mavory/ESP32-Smart-light/Circuit Diagram/ESP32.kicad_sch

## KiCad design Circuit Diagram/ESP32.kicad_sch (2026-01-19)

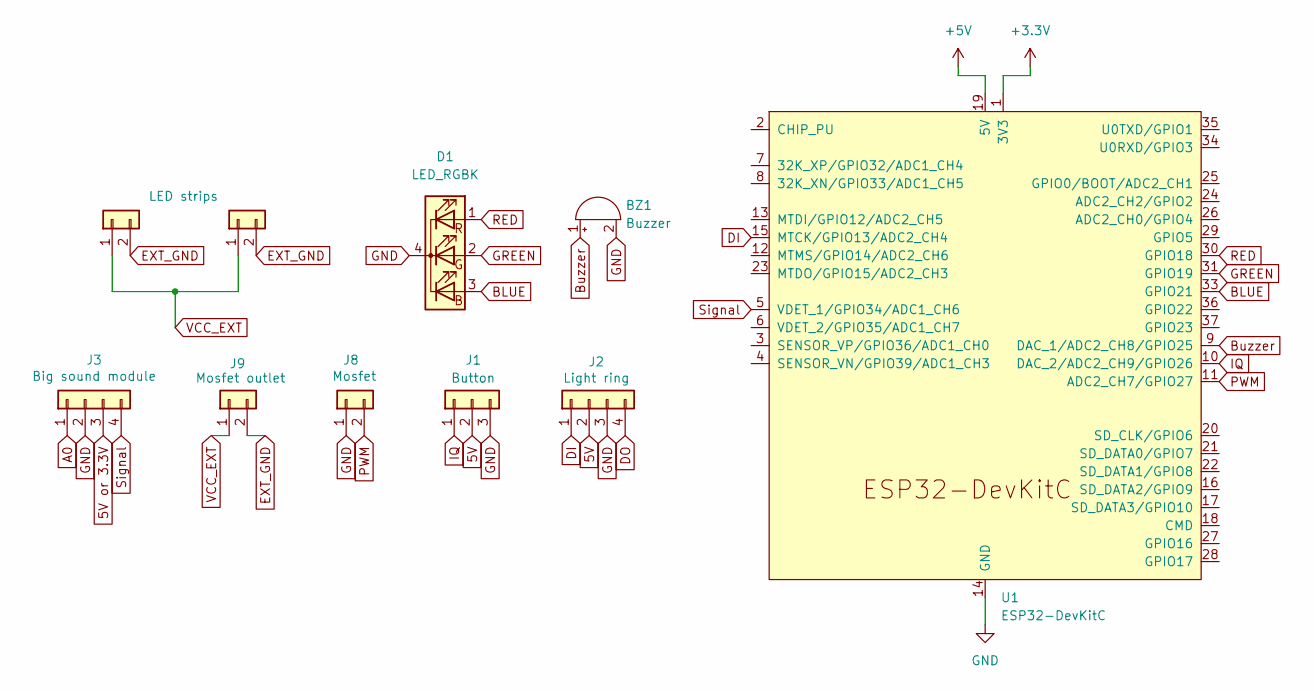
[picture p24: schematic ESP32.kicad_sch]

Parts:
BZ1: Buzzer
D1: LED_RGBK
J1: Button
J2: Light ring
J3: Big sound module
J6: LED strips
J7: Conn_01x02
J8: Mosfet
J9: Mosfet outlet
U1: ESP32-DevKitC

Connections:
5V: J1.2, J2.2
5V or 3.3V: J3.3
+3.3V: U1.1 (3V3)
+5V: U1.19 (5V)
A0: J3.1
BLUE: D1.3 (BA), U1.33 (GPIO21)
Buzzer: BZ1.1 (+), U1.9 (DAC_1/ADC2_CH8/GPIO25)
DI: J2.1, U1.15 (MTCK/GPIO13/ADC2_CH4)
DO: J2.4
EXT_GND: J6.2, J7.2, J9.2
GND: BZ1.2 (-), D1.4 (K), J1.3, J2.3, J3.2, J8.1, U1.14 (GND), U1.32 (GND), U1.38 (GND)
GREEN: D1.2 (GA), U1.31 (GPIO19)
IQ: J1.1, U1.10 (DAC_2/ADC2_CH9/GPIO26)
PWM: J8.2, U1.11 (ADC2_CH7/GPIO27)
RED: D1.1 (RA), U1.30 (GPIO18)
Signal: J3.4, U1.5 (VDET_1/GPIO34/ADC1_CH6)
VCC_EXT: J6.1, J7.1, J9.1
