mavory/ESP32-Smart-light/Photos/20260118_110145.jpg

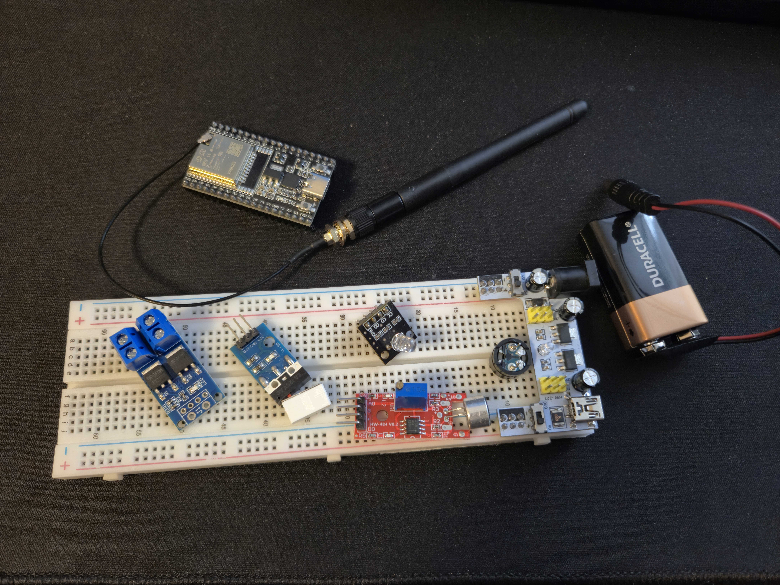
Photos/20260118_110145.jpg
