mavory/ESP32-Smart-light/Photos/20260118_213228.jpg

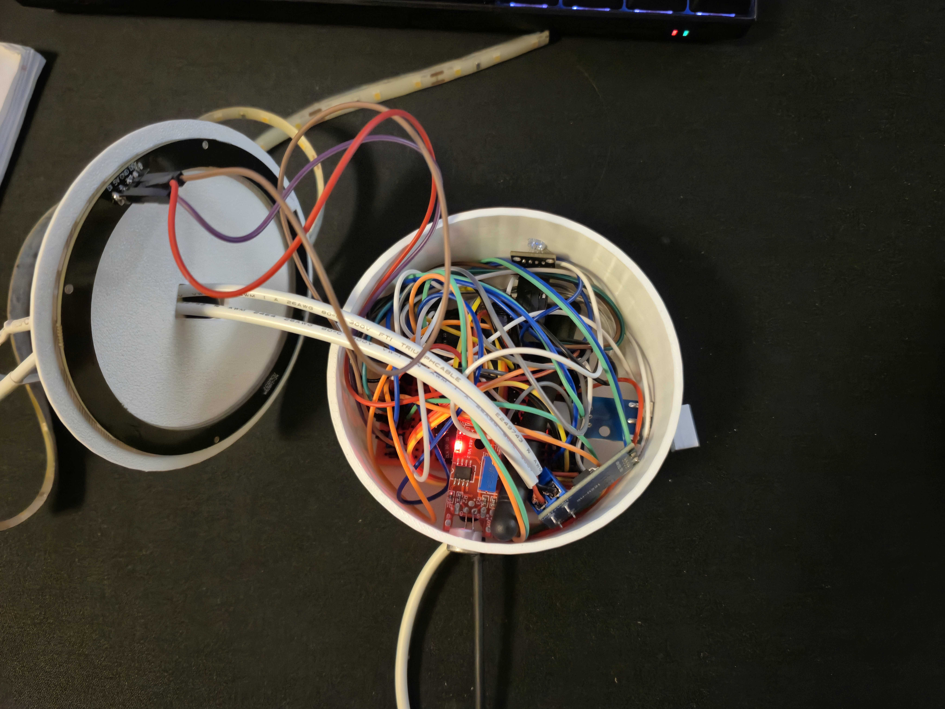
Photos/20260118_213228.jpg
