mavory/ESP32-Smart-light/Photos/20260119_094715 (1).jpg

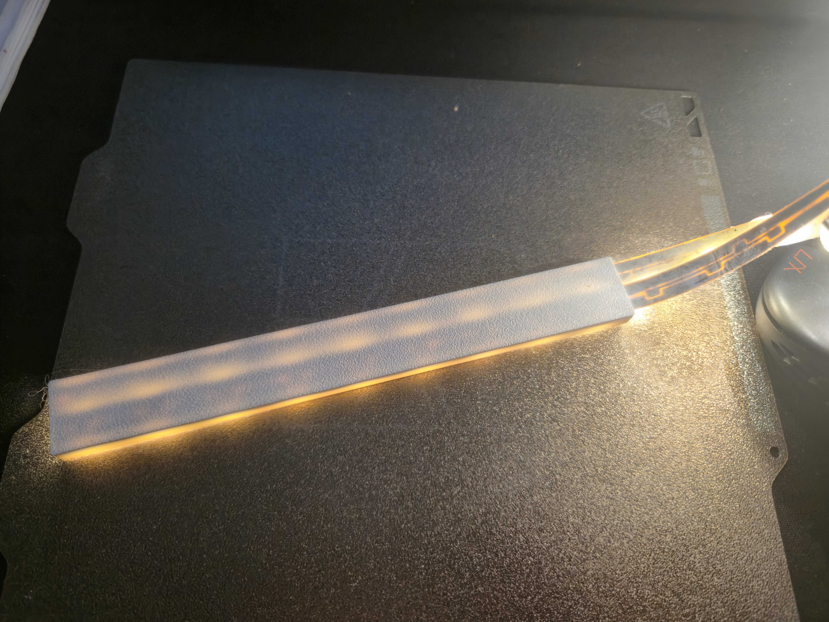
Photos/20260119_094715 (1).jpg
