mavory/ESP32-Smart-light/Photos/20260119_102135.jpg

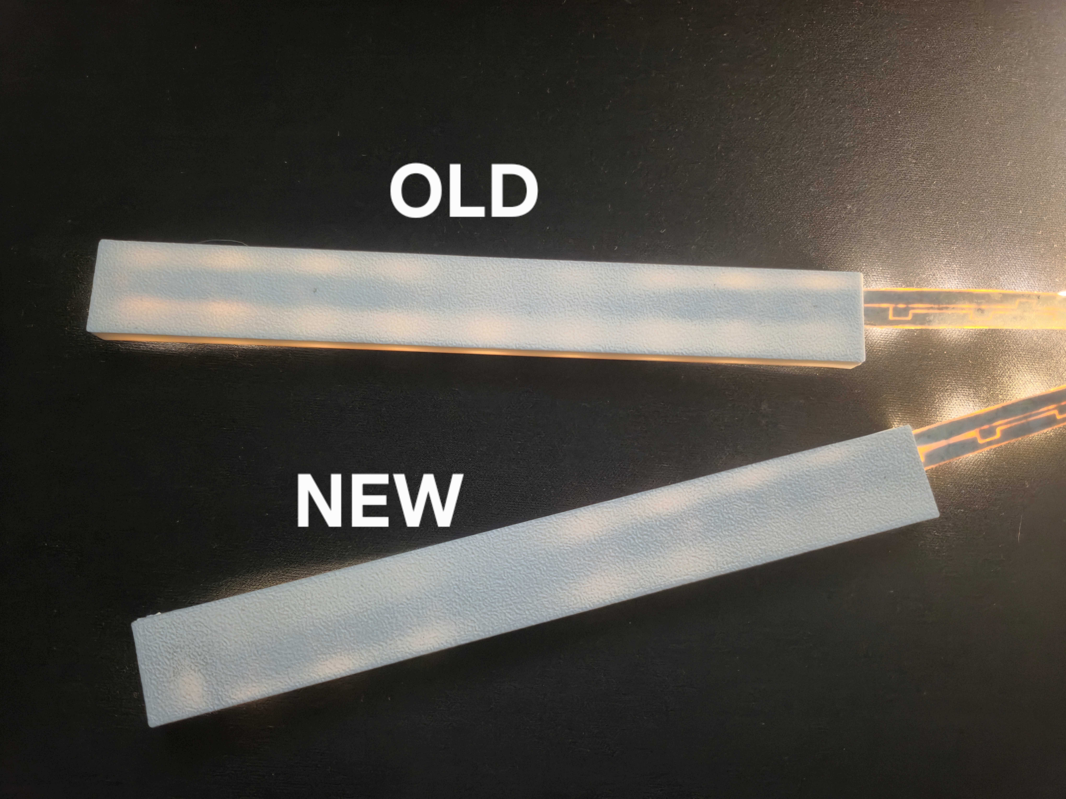
Photos/20260119_102135.jpg
