mavory/ESP32-Smart-light/Photos/20260119_114646 (1).jpg

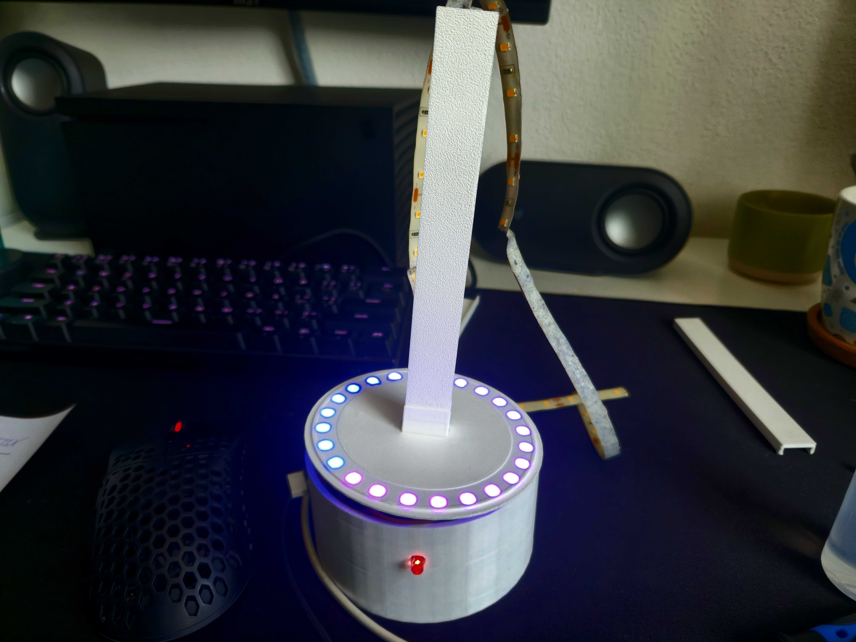
Photos/20260119_114646 (1).jpg
