mavory/ESP32-Smart-light/Photos/20260119_122217.jpg

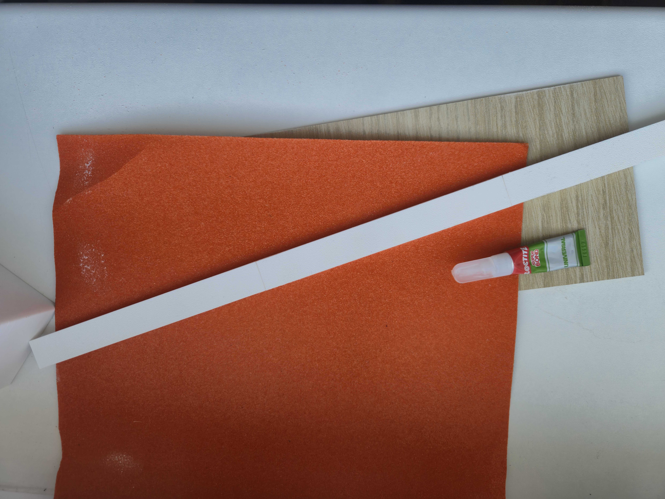
Photos/20260119_122217.jpg
