mavory/ESP32-Smart-light/Photos/20260119_123537.jpg

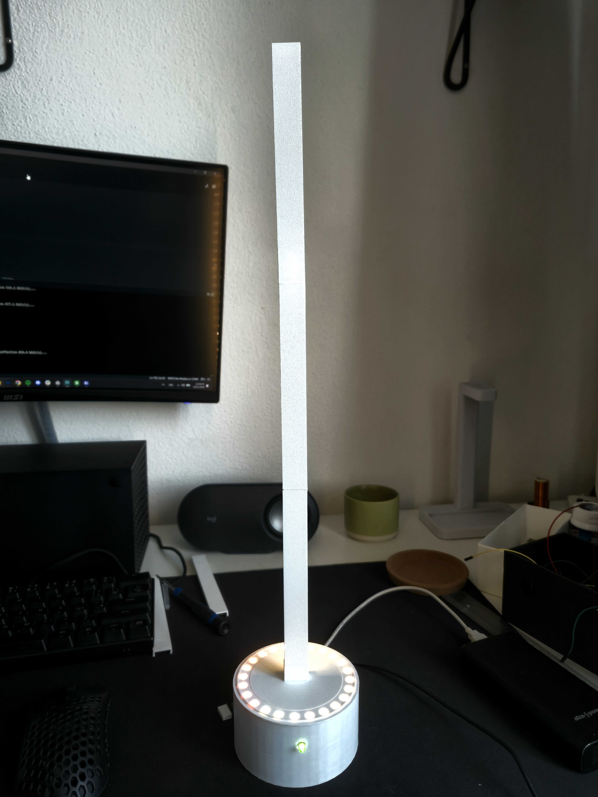
Photos/20260119_123537.jpg
