mavory/ESP32-Smart-light/Photos/1000023968.jpg

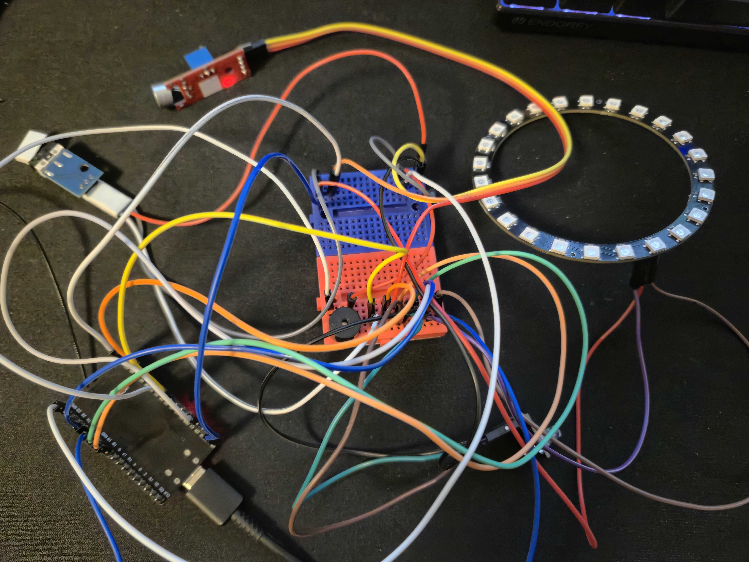
Photos/1000023968.jpg
