mavory/ESP32-Smart-light/Photos/1000023970.jpg

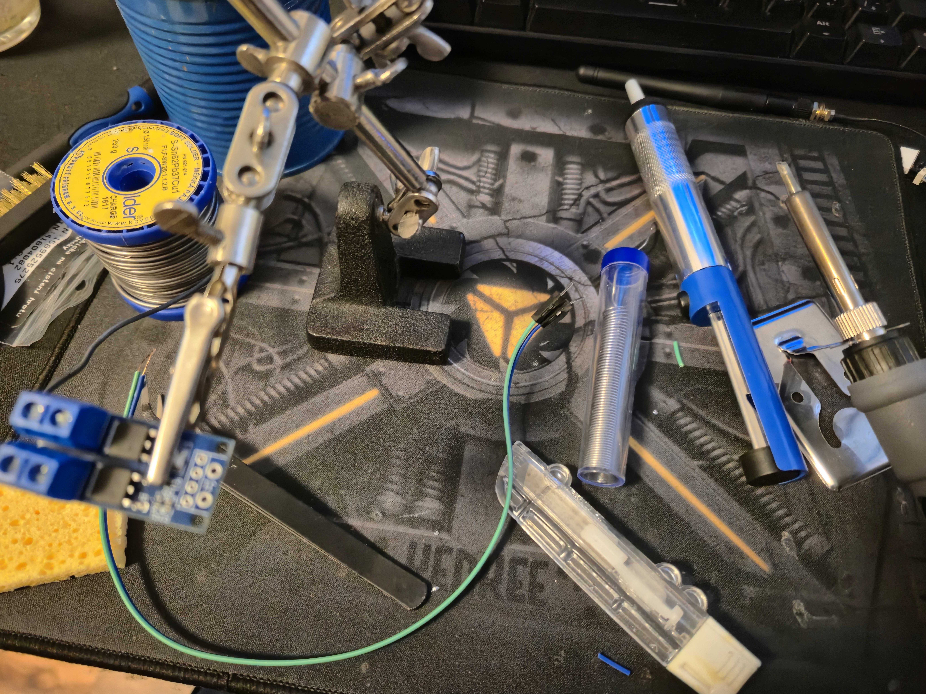
Photos/1000023970.jpg
