mavory/ESP32-Smart-light/Photos/1000023972.jpg

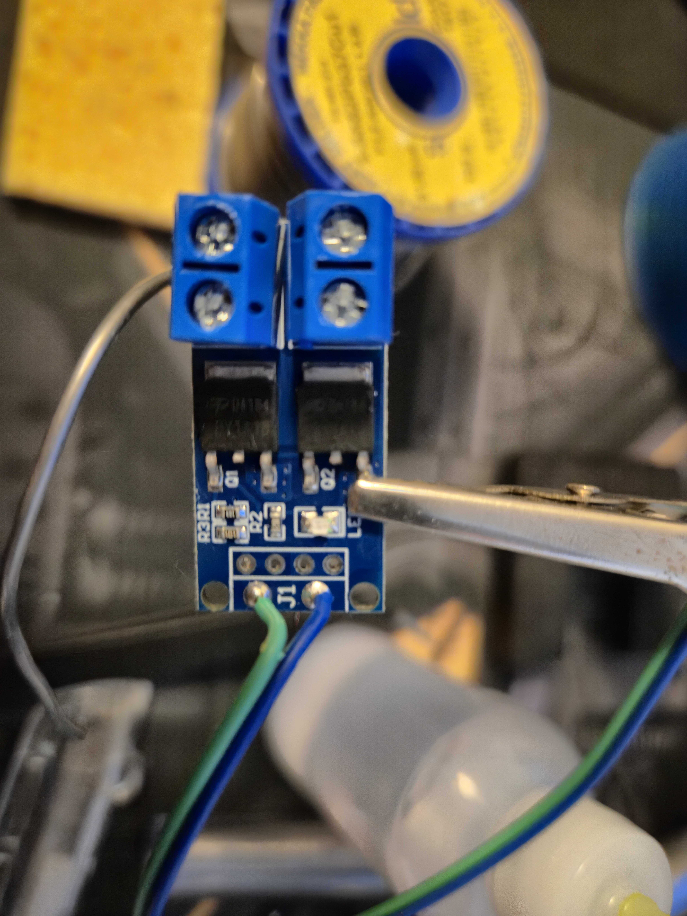
Photos/1000023972.jpg
