mavory/ESP32-Smart-light/Photos/1000023974.jpg

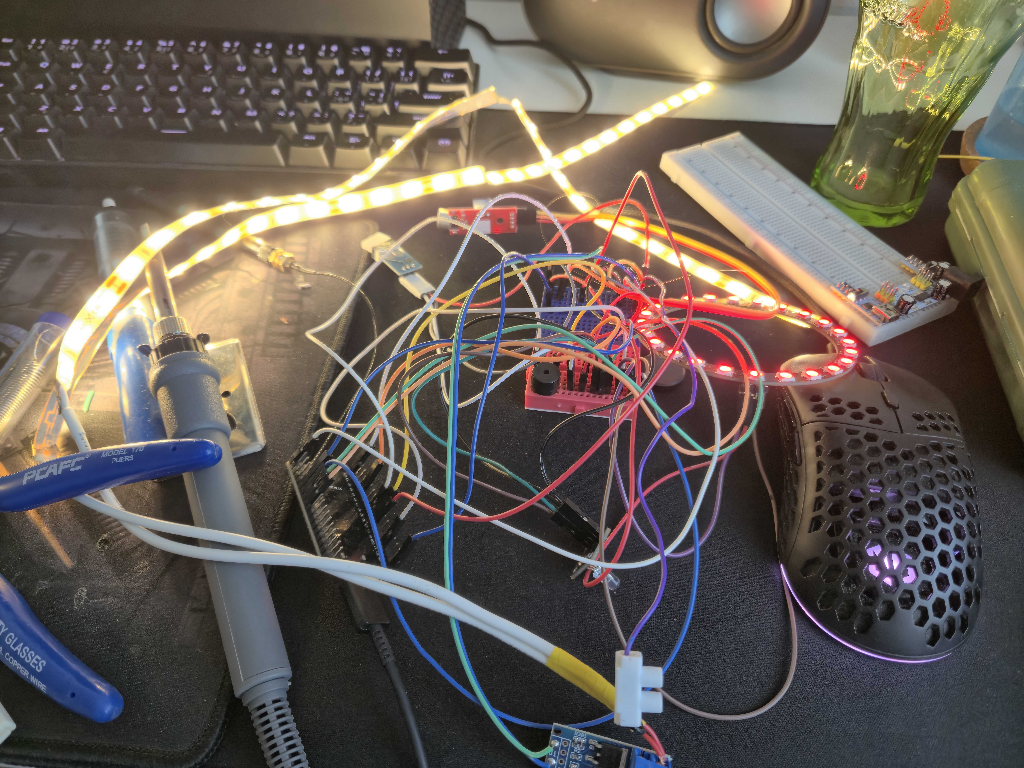
Photos/1000023974.jpg
