mavory/ESP32-Smart-light/Photos/1000023976.jpg

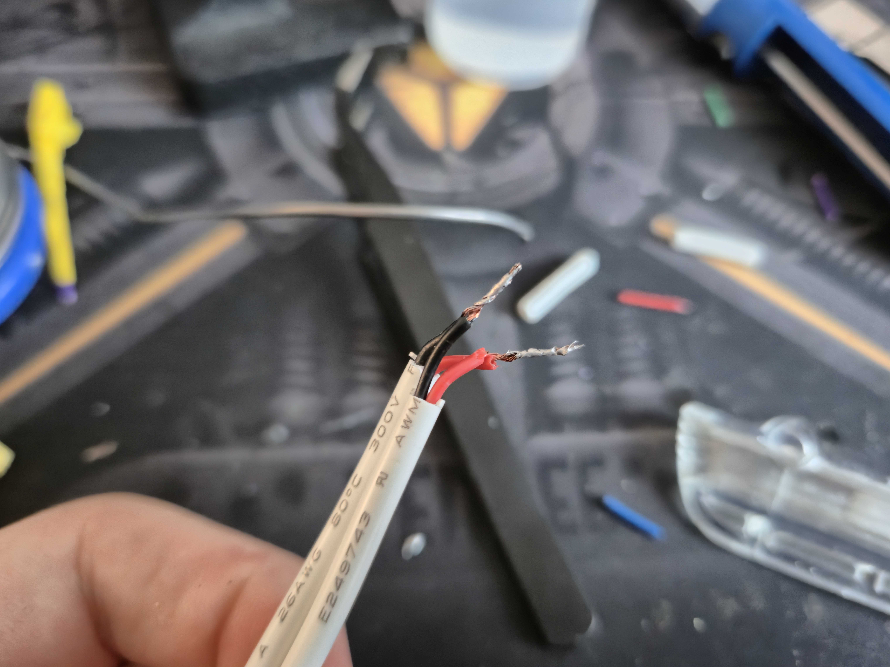
Photos/1000023976.jpg
