mavory/ESP32-Smart-light/Photos/1000023977.jpg

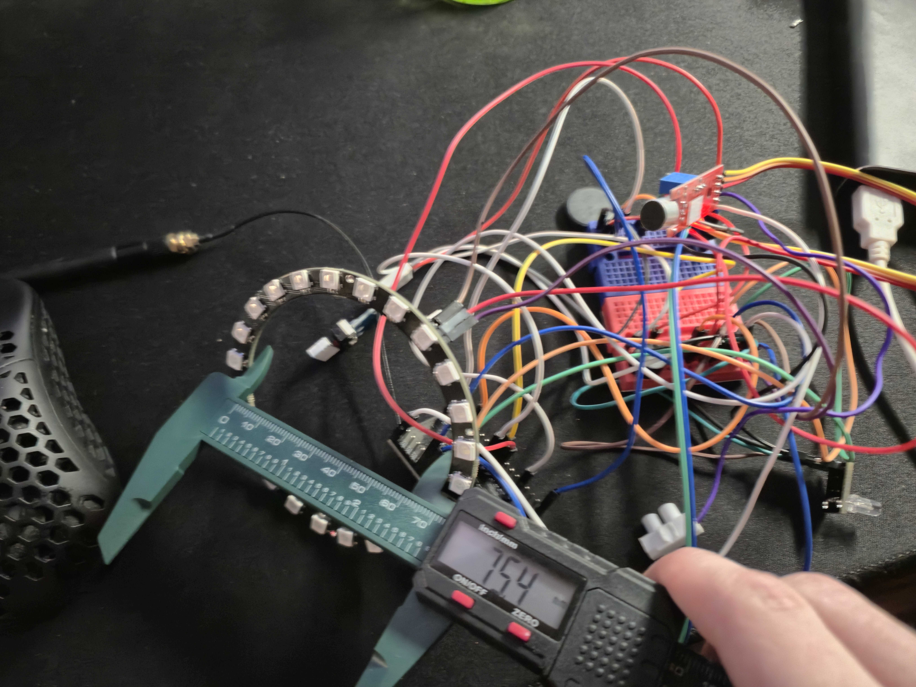
Photos/1000023977.jpg
